nekoewen/peridot-steno/PCB/1.jpg

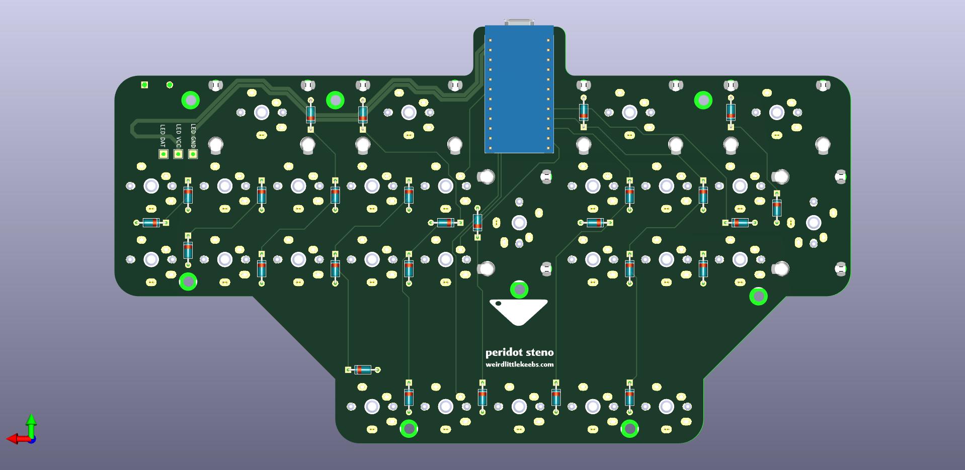
PCB/1.jpg
