nekoewen/peridot-steno/PCB/2.jpg

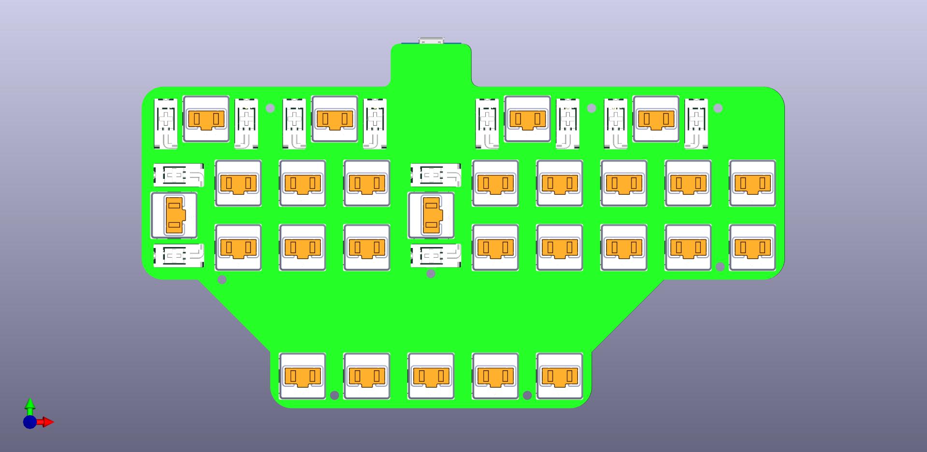
PCB/2.jpg
