nekoewen/peridot-steno/PCB/3.jpg

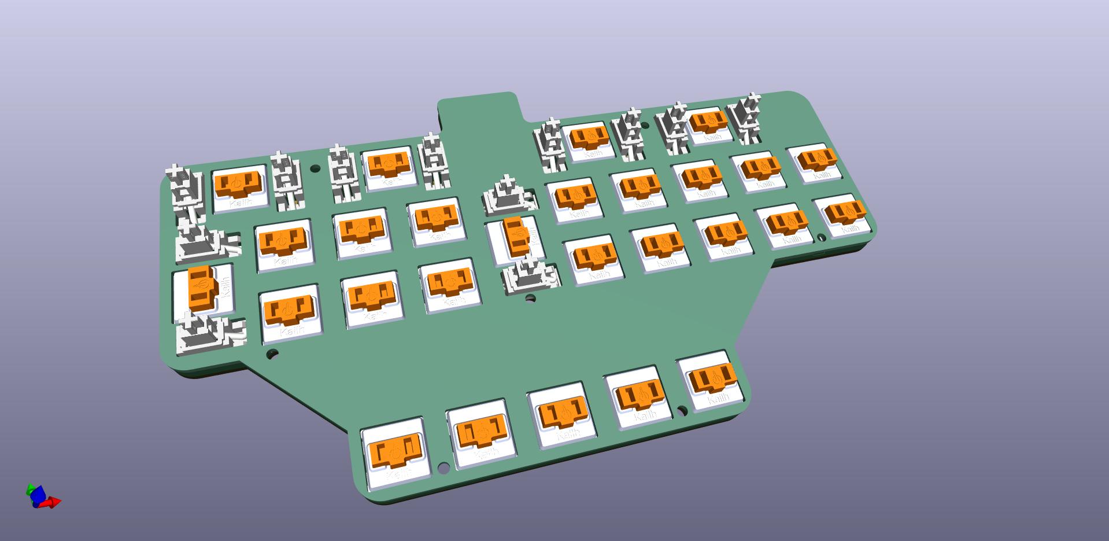
PCB/3.jpg
