nekoewen/peridot-steno/PCB/4.jpg

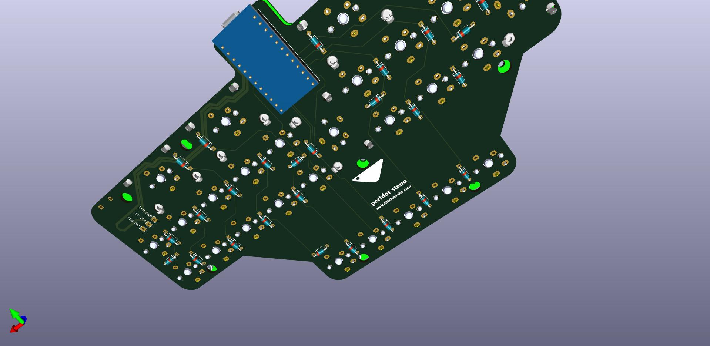
PCB/4.jpg
