nekoewen/peridot-steno/PCB/5.jpg

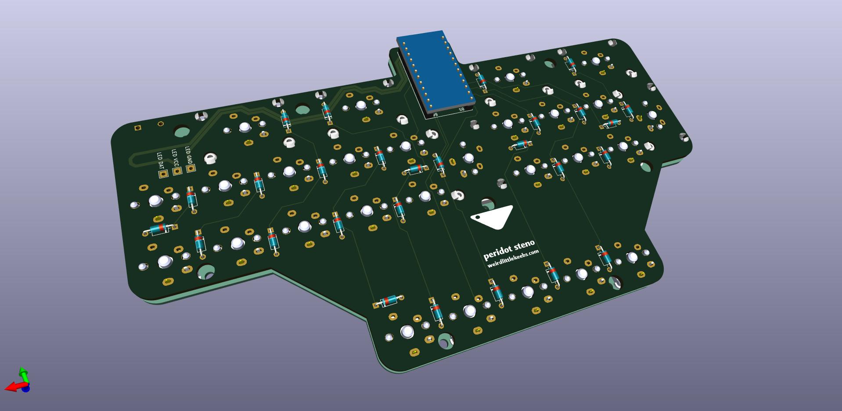
PCB/5.jpg
